Connor205/B-I-K-E/Python/img/Table.png

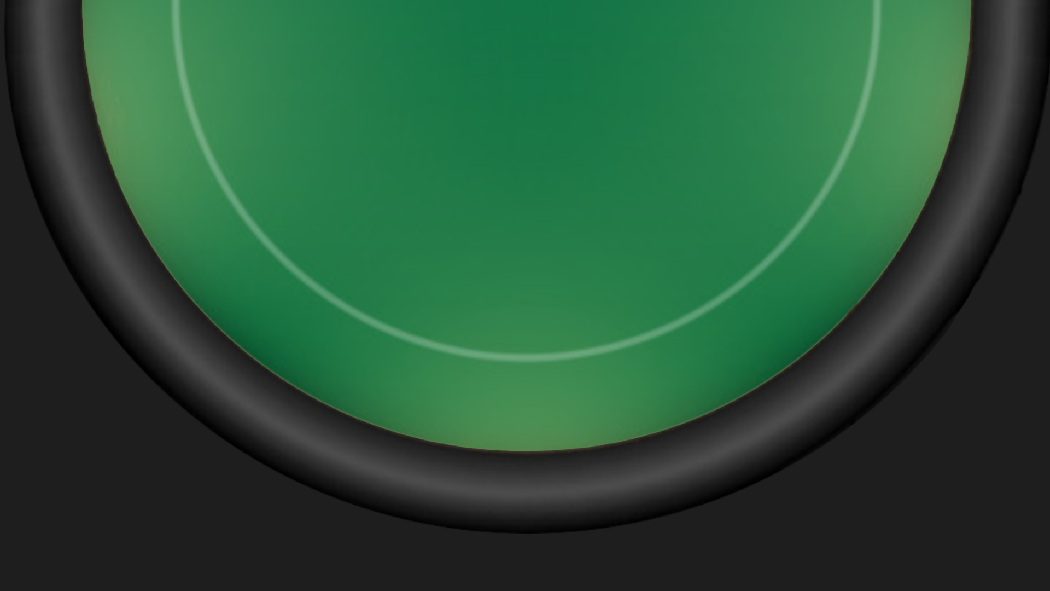
Python/img/Table.png
