Connor205/B-I-K-E/Python/img/card_back_black.png

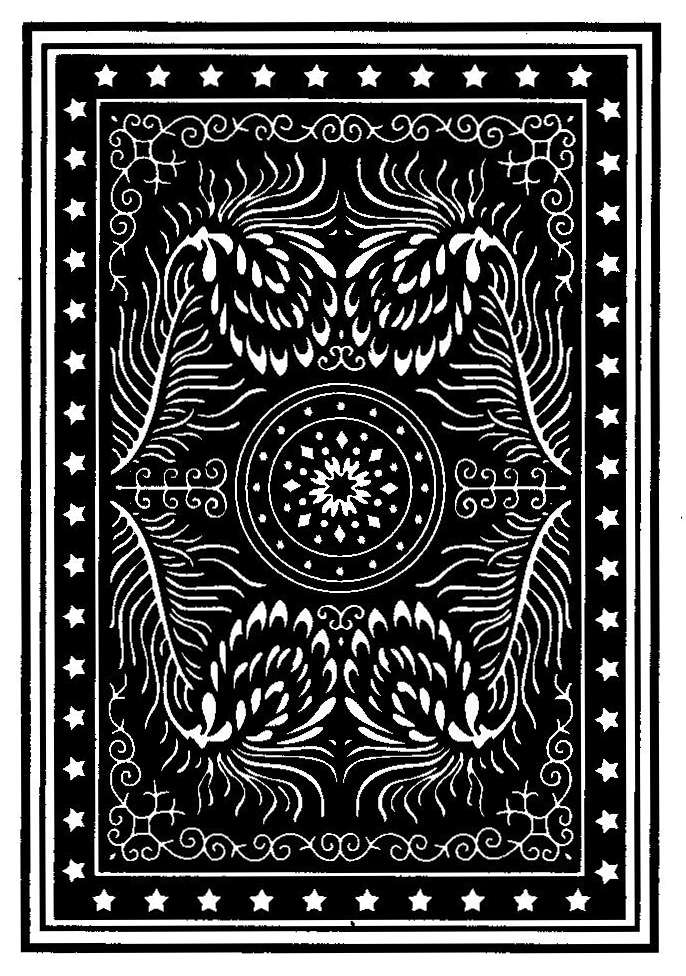
Python/img/card_back_black.png
