Connor205/B-I-K-E/Python/img/card_back_red.png

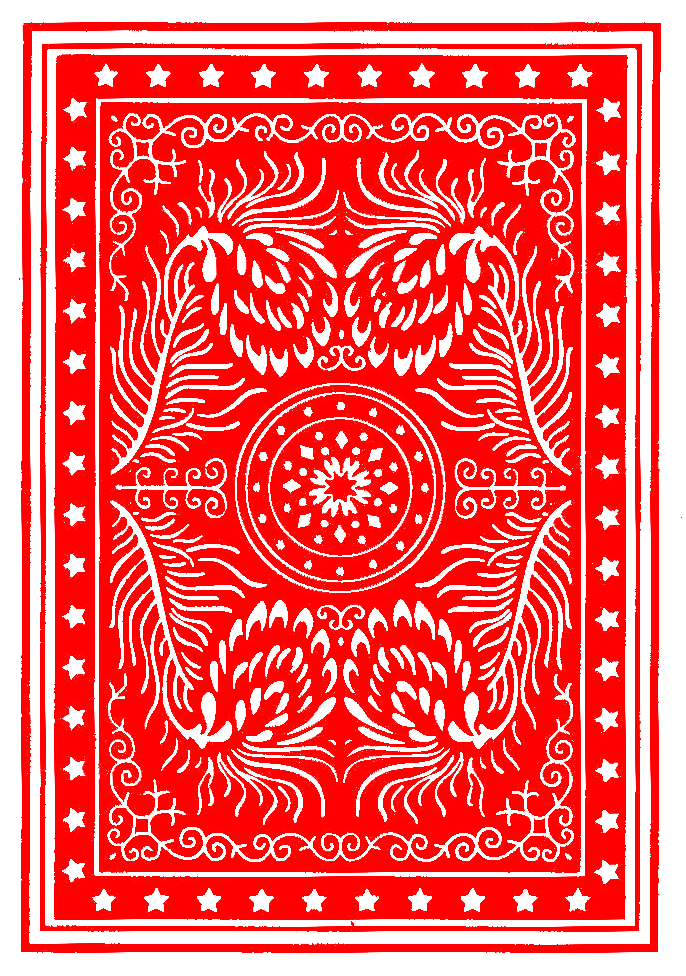
Python/img/card_back_red.png
