Connor205/B-I-K-E/Python/img/popup_window.png

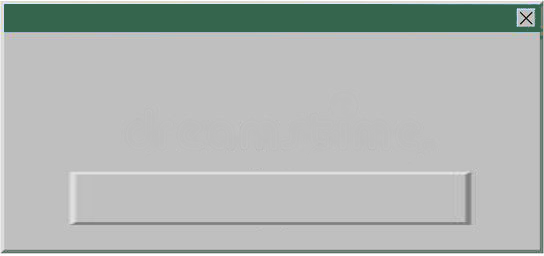
Python/img/popup_window.png
