Connor205/B-I-K-E/Python/Enums.py

from enum import Enum


class Seat(Enum):
    """An Enum representing a seat number at the poker table."""
    ONE = 1
    TWO = 2
    THREE = 3
    FOUR = 4
    
    def __eq__(self, __value: object) -> bool:
        if isinstance(__value, Seat):
            return self.value == __value.value
        return False
    
    def __hash__(self) -> int:
        return hash(self.value)
    
    def __lt__(self, other):
        if isinstance(other, Seat):
            return self.value < other.value
        return NotImplemented
    
    def __str__(self) -> str:
        return f"Seat {self.value}"


class Suit(Enum):
    """An Enum representing a card suit."""
    HEART = 1
    SPADE = 2
    CLUB = 3
    DIAMOND = 4

    def __eq__(self, __value: object) -> bool:
        if isinstance(__value, Suit):
            return self.value == __value.value
        return False
    
    def __hash__(self) -> int:
        return hash(self.value)
    
    def __str__(self) -> str:
        return f"{self.name}"


class Value(Enum):
    """An Enum representing a card value."""
    TWO = 2
    THREE = 3
    FOUR = 4
    FIVE = 5
    SIX = 6
    SEVEN = 7
    EIGHT = 8
    NINE = 9
    TEN = 10
    JACK = 11
    QUEEN = 12
    KING = 13
    ACE = 14

    def compare(self, other: 'Value') -> int:
        """Compares another Value with this Value.

        Args:
            other (Value): Other Value to compare.

        Returns:
            int: Negative value if this Value is of lesser value.
            Positive value if this Value is of greater value.
            0 if the same Value value.
        """
        return self.value - other.value

    def __lt__(self, other):
        if isinstance(other, Value):
            return self.value < other.value
        return NotImplemented
    
    def __eq__(self, __value: object) -> bool:
        if isinstance(__value, Value):
            return self.value == __value.value
        return False
    
    def __hash__(self) -> int:
        return hash(self.value)
    
    def __sub__(self, other):
        if isinstance(other, Value):
            return self.value - other.value
        return NotImplemented
    
    def __str__(self) -> str:
        return f"{self.name}"

class HandRanking(Enum):
    """An Enum representing poker hand rankings."""
    HIGH_CARD = 1
    PAIR = 2
    TWO_PAIR = 3
    THREE_OF_A_KIND = 4
    STRAIGHT = 5
    FLUSH = 6
    FULL_HOUSE = 7
    FOUR_OF_A_KIND = 8
    STRAIGHT_FLUSH = 9
    ROYAL_FLUSH = 10

    def compare(self, other: 'HandRanking') -> int:
        """Compares another HandRanking with this HandRanking.

        Args:
            other (HandRanking): Other HandRanking to compare.

        Returns:
            int: Negative value if this HandRanking is of lesser value.
            Positive value if this HandRanking is of greater value.
            0 if the same HandRanking value.
        """
        return self.value - other.value
    
    def __lt__(self, other):
        if isinstance(other, HandRanking):
            return self.value < other.value
        return NotImplemented
    
    def __eq__(self, __value: object) -> bool:
        if isinstance(__value, HandRanking):
            return self.value == __value.value
        return NotImplemented
    
    def __hash__(self) -> int:
        return hash(self.value)
    
    def __str__(self) -> str:
        if self == HandRanking.HIGH_CARD:
            return "High Card"
        elif self == HandRanking.PAIR:
            return "Pair"
        elif self == HandRanking.TWO_PAIR:
            return "Two Pair"
        elif self == HandRanking.THREE_OF_A_KIND:
            return "Three of a Kind"
        elif self == HandRanking.STRAIGHT:
            return "Straight"
        elif self == HandRanking.FLUSH:
            return "Flush"
        elif self == HandRanking.FULL_HOUSE:
            return "Full House"
        elif self == HandRanking.FOUR_OF_A_KIND:
            return "Four of a Kind"
        elif self == HandRanking.STRAIGHT_FLUSH:
            return "Straight Flush"
        elif self == HandRanking.ROYAL_FLUSH:
            return "Royal Flush"
        else:
            return "Unknown"


class GameState(Enum):
    """An Enum representing the states of a poker game."""
    PREPARING = 1
    PREFLOP = 2
    FLOP = 3
    TURN = 4
    RIVER = 5
    SHOWDOWN = 6
    POSTHAND = 7

class Button(Enum):
    """An Enum representing the buttons the players have access to."""
    FOLD = 1
    CHECK = 2
    CALL = 3
    BET = 4
    WHITE_CHIP = 5
    BLUE_CHIP = 6
    RED_CHIP = 7
    SETTINGS = 8
    SHUFFLECONFIRM = 9
    DEALCONFIRM = 10

class Blind(Enum):
    """An Enum representing the blinds."""
    SB = 1
    BB = 2
